sam0737/PopnConvertibleAsc/Firmware/Descriptors.c

/*
  Pop'n Convertible Arcade Style Controller Project
 
  Copyright 2011 Sam Wong (Sam /@/ hellosam /./ net)

  This work is licensed under the Creative Commons Attribution 3.0 
  Hong Kong License. 

  To view a copy of this license, visit 
  http://creativecommons.org/licenses/by/3.0/hk/ or send a letter to 
  Creative Commons, 444 Castro Street, Suite 900, 
  Mountain View, California, 94041, USA.

  --
  Code is based on the following LUFA Demo project
    [Demos\Device\ClassDriver\Keyboard]:

  Copyright 2011  Dean Camera (dean [at] fourwalledcubicle [dot] com)

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
  The author disclaim all warranties with regard to this
  software, including all implied warranties of merchantability
  and fitness.  In no event shall the author be liable for any
  special, indirect or consequential damages or any damages
  whatsoever resulting from loss of use, data or profits, whether
  in an action of contract, negligence or other tortious action,
  arising out of or in connection with the use or performance of
  this software.
*/

#include "Descriptors.h"
#include <avr/pgmspace.h>

/** HID class report descriptor. 
 *
 * IN Report:
 * Byte 1: 
 *      Bit status of key 1 to 8 (Active High)
 * Byte 2: 
 *      Bit status of key 9 (Active High)
 *      7 reserved bits.
 */
const USB_Descriptor_HIDReport_Datatype_t PROGMEM KeyboardReport[] =
{
    0x05, 0x01,                    // USAGE_PAGE (Generic Desktop)
    0x09, 0x06,                    // USAGE (Keyboard)
    0xa1, 0x01,                    // COLLECTION (Application)

    0x05, 0x07,                    //   USAGE_PAGE (Keyboard)
    0x19, 0x1E,                    //   USAGE_MINIMUM (Keyboard 1 and !)
    0x29, 0x26,                    //   USAGE_MAXIMUM (Keyboard 9 and ()
    0x15, 0x00,                    //   LOGICAL_MINIMUM (0)
    0x25, 0x01,                    //   LOGICAL_MAXIMUM (1)
    0x75, 0x01,                    //   REPORT_SIZE (1)
    0x95, 0x09,                    //   REPORT_COUNT (9)
    0x81, 0x02,                    //   INPUT (Data,Var,Abs)
    0x75, 0x07,                    //   REPORT_SIZE (7)
    0x95, 0x01,                    //   REPORT_COUNT (1)
    0x81, 0x03,                    //   INPUT (Cnst,Var,Abs) 
    0xc0                           // END_COLLECTION
};

/** Device descriptor structure.
 */
const USB_Descriptor_Device_t PROGMEM DeviceDescriptor =
{
    .Header                 = {.Size = sizeof(USB_Descriptor_Device_t), .Type = DTYPE_Device},

    .USBSpecification       = VERSION_BCD(01.10),
    .Class                  = USB_CSCP_NoDeviceClass,
    .SubClass               = USB_CSCP_NoDeviceSubclass,
    .Protocol               = USB_CSCP_NoDeviceProtocol,

    .Endpoint0Size          = FIXED_CONTROL_ENDPOINT_SIZE,

    .VendorID               = 0x03EB,
    .ProductID              = 0x2042,
    .ReleaseNumber          = VERSION_BCD(00.01),

    .ManufacturerStrIndex   = 0x01,
    .ProductStrIndex        = 0x02,
    .SerialNumStrIndex      = NO_DESCRIPTOR,

    .NumberOfConfigurations = FIXED_NUM_CONFIGURATIONS
};

/** Configuration descriptor structure.
 */
const USB_Descriptor_Configuration_t PROGMEM ConfigurationDescriptor =
{
    .Config =
        {
            .Header                 = {.Size = sizeof(USB_Descriptor_Configuration_Header_t), .Type = DTYPE_Configuration},

            .TotalConfigurationSize = sizeof(USB_Descriptor_Configuration_t),
            .TotalInterfaces        = 1,

            .ConfigurationNumber    = 1,
            .ConfigurationStrIndex  = NO_DESCRIPTOR,

            .ConfigAttributes       = (USB_CONFIG_ATTR_BUSPOWERED | USB_CONFIG_ATTR_SELFPOWERED),

            .MaxPowerConsumption    = USB_CONFIG_POWER_MA(300)
        },

    .HID_Interface =
        {
            .Header                 = {.Size = sizeof(USB_Descriptor_Interface_t), .Type = DTYPE_Interface},

            .InterfaceNumber        = 0x00,
            .AlternateSetting       = 0x00,

            .TotalEndpoints         = 1,

            .Class                  = HID_CSCP_HIDClass,
            .SubClass               = HID_CSCP_NonBootSubclass,
            .Protocol               = HID_CSCP_NonBootProtocol,

            .InterfaceStrIndex      = NO_DESCRIPTOR
        },

    .HID_KeyboardHID =
        {
            .Header                 = {.Size = sizeof(USB_HID_Descriptor_HID_t), .Type = HID_DTYPE_HID},

            .HIDSpec                = VERSION_BCD(01.11),
            .CountryCode            = 0x00,
            .TotalReportDescriptors = 1,
            .HIDReportType          = HID_DTYPE_Report,
            .HIDReportLength        = sizeof(KeyboardReport)
        },

    .HID_ReportINEndpoint =
        {
            .Header                 = {.Size = sizeof(USB_Descriptor_Endpoint_t), .Type = DTYPE_Endpoint},

            .EndpointAddress        = (ENDPOINT_DESCRIPTOR_DIR_IN | DEVICE_ENDPOINT_NUM),
            .Attributes             = (EP_TYPE_INTERRUPT | ENDPOINT_ATTR_NO_SYNC | ENDPOINT_USAGE_DATA),
            .EndpointSize           = DEVICE_ENDPOINT_SIZE,
            .PollingIntervalMS      = 0x01
        },
};

/** Language descriptor structure. 
 */
const USB_Descriptor_String_t PROGMEM LanguageString =
{
    .Header                 = {.Size = USB_STRING_LEN(1), .Type = DTYPE_String},
    .UnicodeString          = {LANGUAGE_ID_ENG}
};

/** Manufacturer descriptor string.
 */
const USB_Descriptor_String_t PROGMEM ManufacturerString =
{
    .Header                 = {.Size = USB_STRING_LEN(8), .Type = DTYPE_String},
    .UnicodeString          = L"Sam Wong"
};

/** Product descriptor string.
 */
const USB_Descriptor_String_t PROGMEM ProductString =
{
    .Header                 = {.Size = USB_STRING_LEN(29), .Type = DTYPE_String},
    .UnicodeString          = L"Pop'n Convertible Asc Project"
};

/** This function is called by the library when in device mode, and must be overridden (see library "USB Descriptors"
 *  documentation) by the application code so that the address and size of a requested descriptor can be given
 *  to the USB library. When the device receives a Get Descriptor request on the control endpoint, this function
 *  is called so that the descriptor details can be passed back and the appropriate descriptor sent back to the
 *  USB host.
 */
uint16_t CALLBACK_USB_GetDescriptor(const uint16_t wValue,
                                    const uint8_t wIndex,
                                    const void** const DescriptorAddress)
{
    const uint8_t  DescriptorType   = (wValue >> 8);
    const uint8_t  DescriptorNumber = (wValue & 0xFF);

    const void* Address = NULL;
    uint16_t    Size    = NO_DESCRIPTOR;

    switch (DescriptorType)
    {
        case DTYPE_Device:
            Address = &DeviceDescriptor;
            Size    = sizeof(USB_Descriptor_Device_t);
            break;
        case DTYPE_Configuration:
            Address = &ConfigurationDescriptor;
            Size    = sizeof(USB_Descriptor_Configuration_t);
            break;
        case DTYPE_String:
            switch (DescriptorNumber)
            {
                case 0x00:
                    Address = &LanguageString;
                    Size    = pgm_read_byte(&LanguageString.Header.Size);
                    break;
                case 0x01:
                    Address = &ManufacturerString;
                    Size    = pgm_read_byte(&ManufacturerString.Header.Size);
                    break;
                case 0x02:
                    Address = &ProductString;
                    Size    = pgm_read_byte(&ProductString.Header.Size);
                    break;
            }

            break;
        case HID_DTYPE_HID:
            Address = &ConfigurationDescriptor.HID_KeyboardHID;
            Size    = sizeof(USB_HID_Descriptor_HID_t);
            break;
        case HID_DTYPE_Report:
            Address = &KeyboardReport;
            Size    = sizeof(KeyboardReport);
            break;
    }

    *DescriptorAddress = Address;
    return Size;
}
